tallman5/diy-utility-drawers/images/4-cab-counter-36.35--finish-height.png

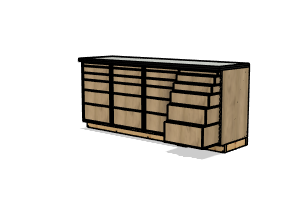
images/4-cab-counter-36.35--finish-height.png
