tallman5/diy-utility-drawers/images/Cabinet Assembly.png

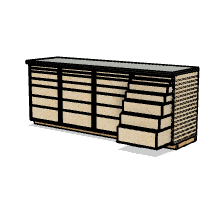
images/Cabinet Assembly.png
