tallman5/diy-utility-drawers/images/cabinet-assembly-v19-render-cropped.png

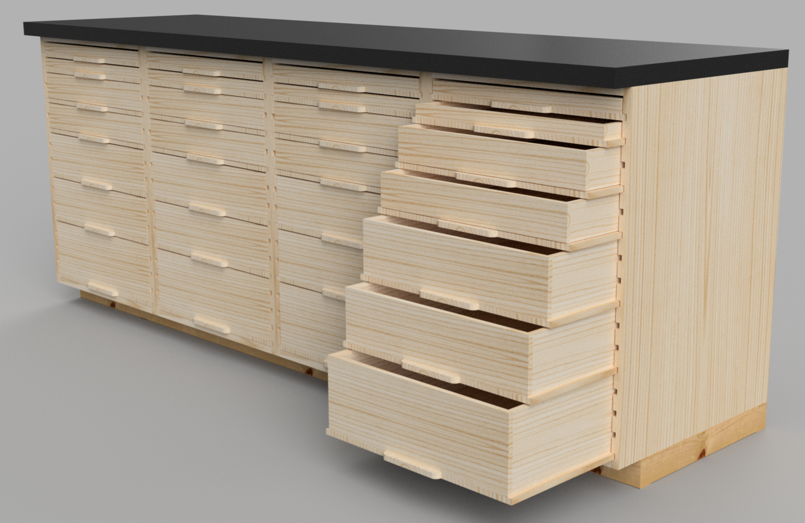
images/cabinet-assembly-v19-render-cropped.png
